mengstr/Rom2k40/Images/Rom2k40-Back-NoParts.png

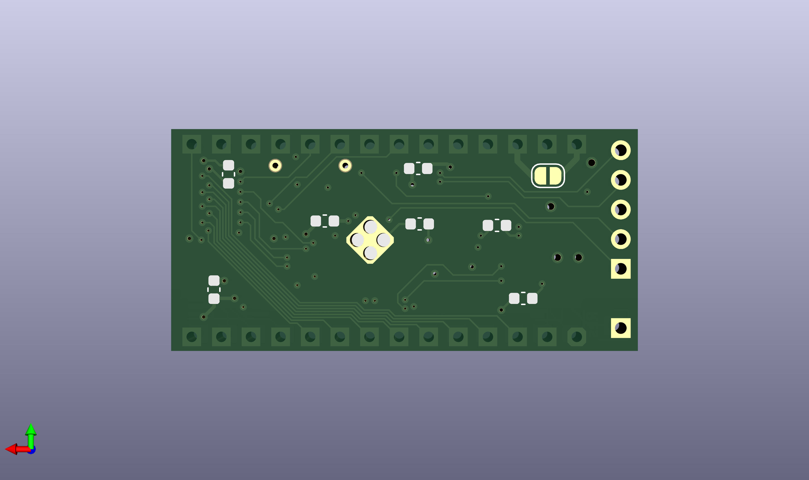
Images/Rom2k40-Back-NoParts.png
